AEFeinstein/Super-2023-Swadge-HW/3D-Print/eggshell clear.png

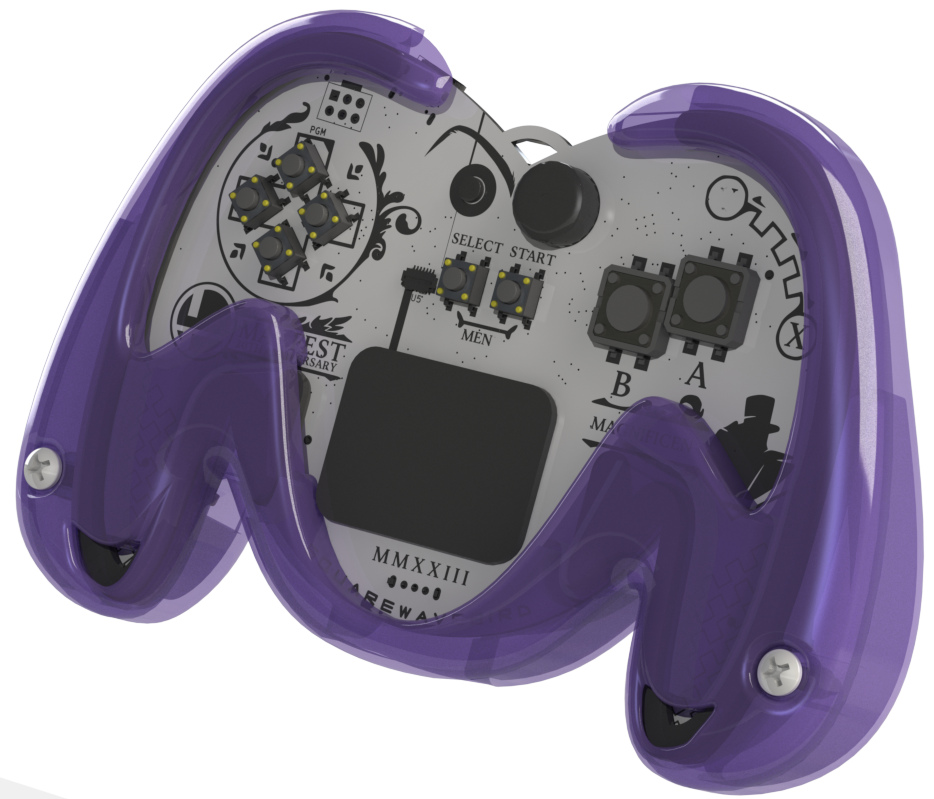
3D-Print/eggshell clear.png
